HTangl/DIDIY-Case/Pictures/Ordering Guide/06.png

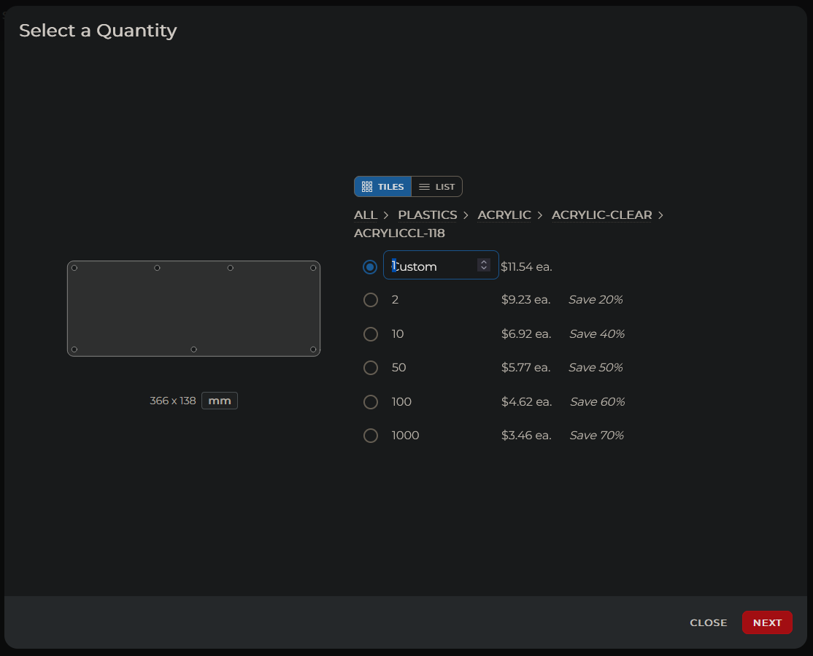
Pictures/Ordering Guide/06.png
