HTangl/DIDIY-Case/Pictures/Ordering Guide/08.png

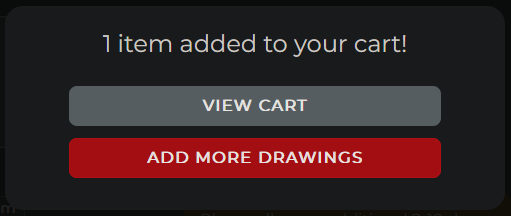
Pictures/Ordering Guide/08.png
